Hanqaqa/Easyduino/Atmega328p Arduino Nano/ProductionFiles/PDFs/Schematic_Page_2.png

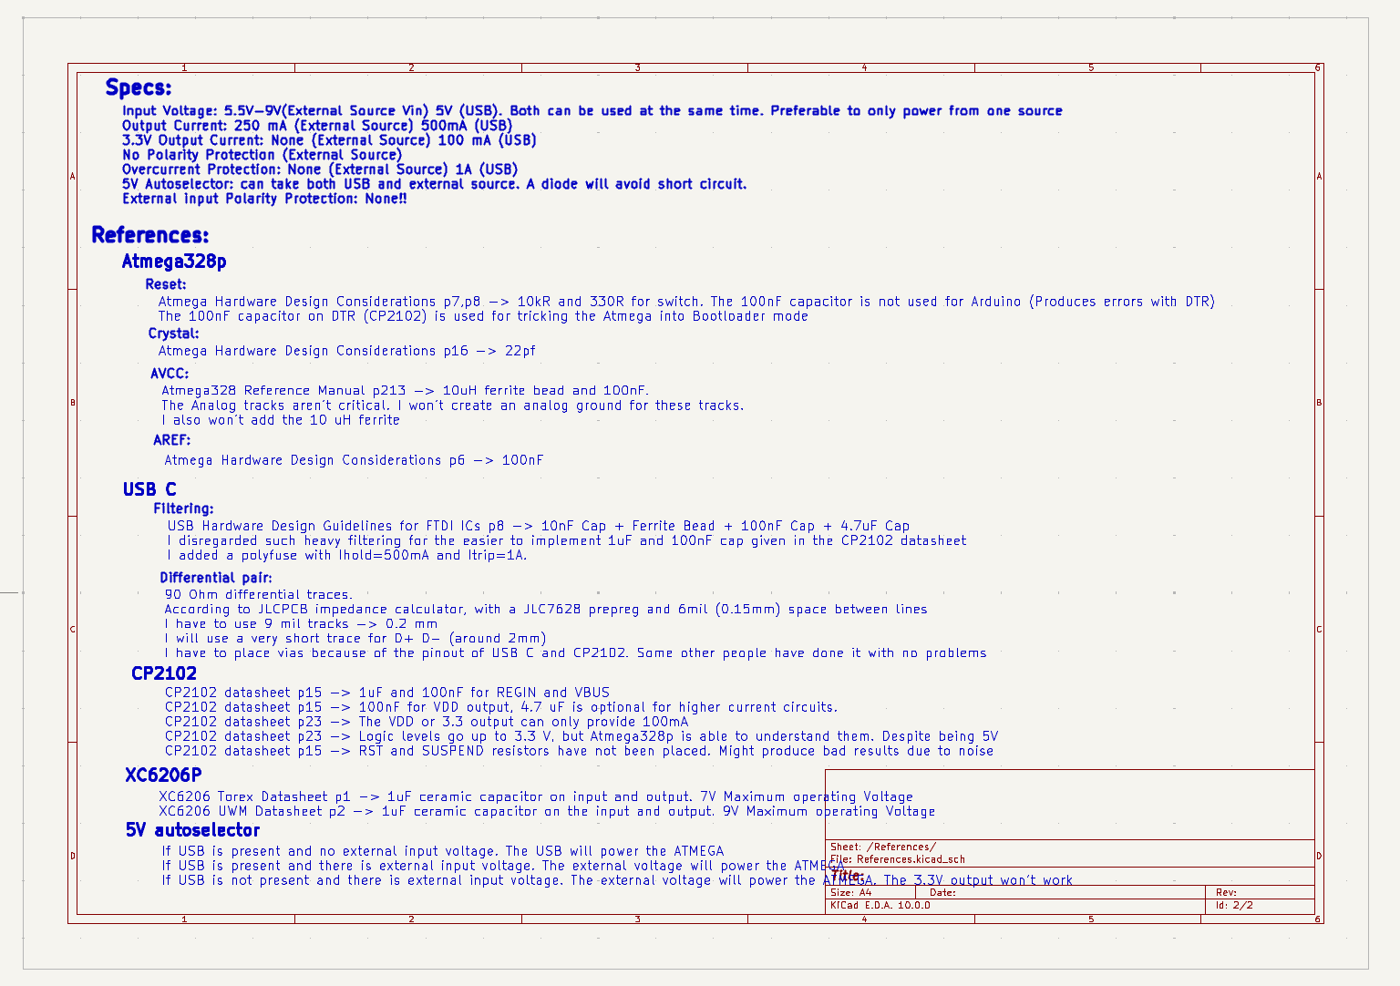
Atmega328p Arduino Nano/ProductionFiles/PDFs/Schematic_Page_2.png
