Hanqaqa/Easyduino/Atmega328p Arduino Nano/ProductionFiles/Photos/Easyduino Nano Bottom.jpg

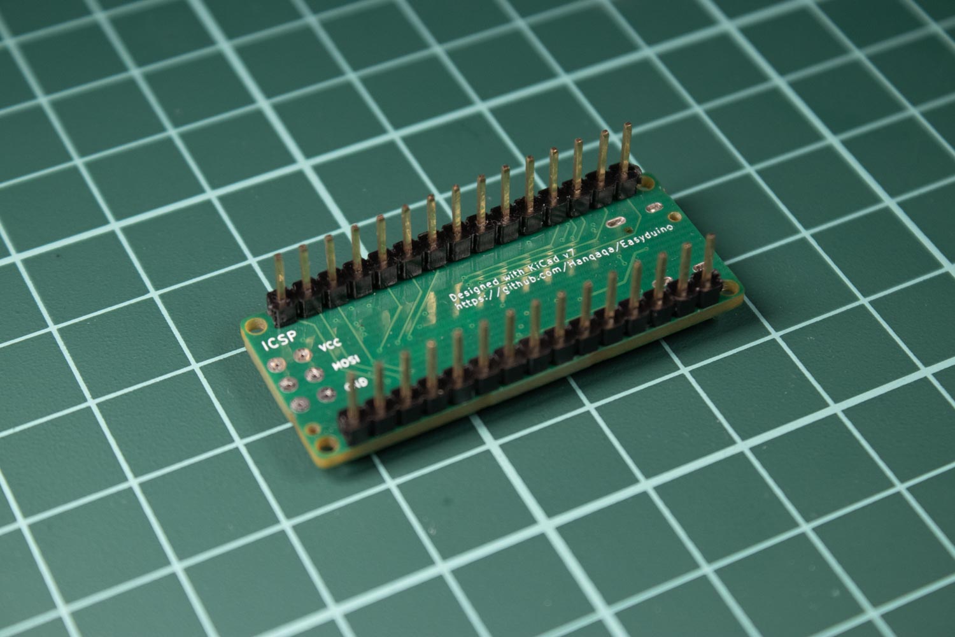
Atmega328p Arduino Nano/ProductionFiles/Photos/Easyduino Nano Bottom.jpg
