Hanqaqa/Easyduino/Atmega328p Arduino Nano/ProductionFiles/Photos/Easyduino Nano Detail 1.jpg

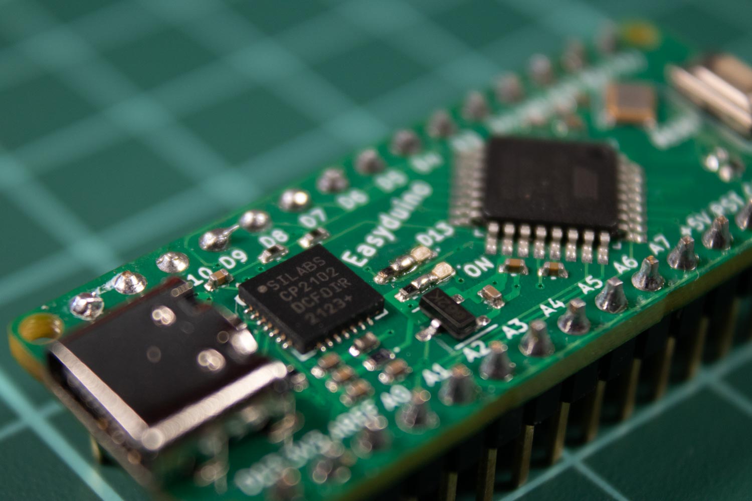
Atmega328p Arduino Nano/ProductionFiles/Photos/Easyduino Nano Detail 1.jpg
