Hanqaqa/Easyduino/Atmega328p Arduino Nano/ProductionFiles/Photos/Easyduino Nano Detail 2.jpg

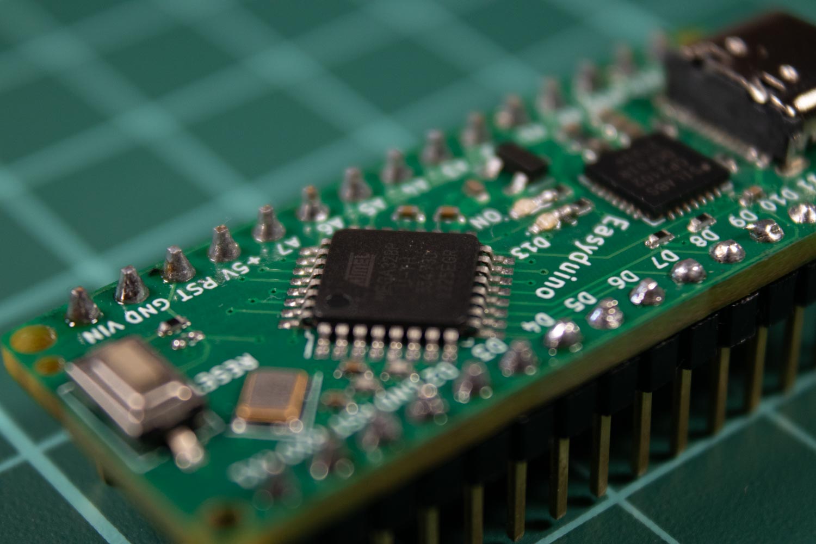
Atmega328p Arduino Nano/ProductionFiles/Photos/Easyduino Nano Detail 2.jpg
