Hanqaqa/Easyduino/Atmega328p Arduino Nano/ProductionFiles/Photos/Easyduino Nano Render Top.jpg

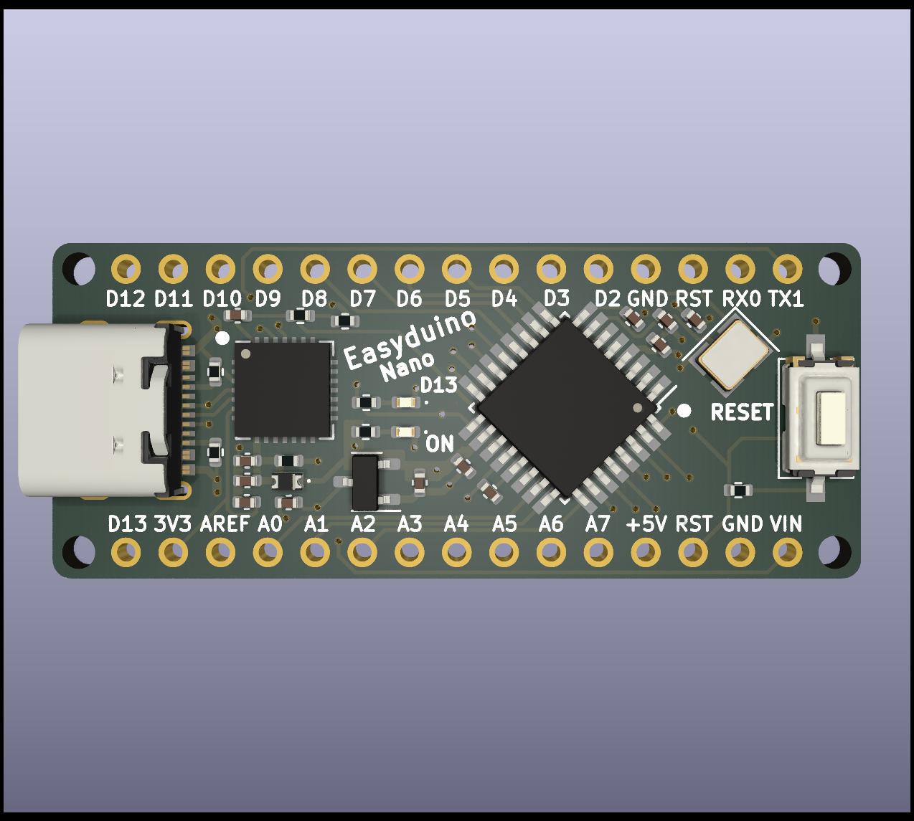
Atmega328p Arduino Nano/ProductionFiles/Photos/Easyduino Nano Render Top.jpg
