Hanqaqa/Easyduino/Atmega328p Arduino Nano/ProductionFiles/Photos/Easyduino Nano Top.jpg

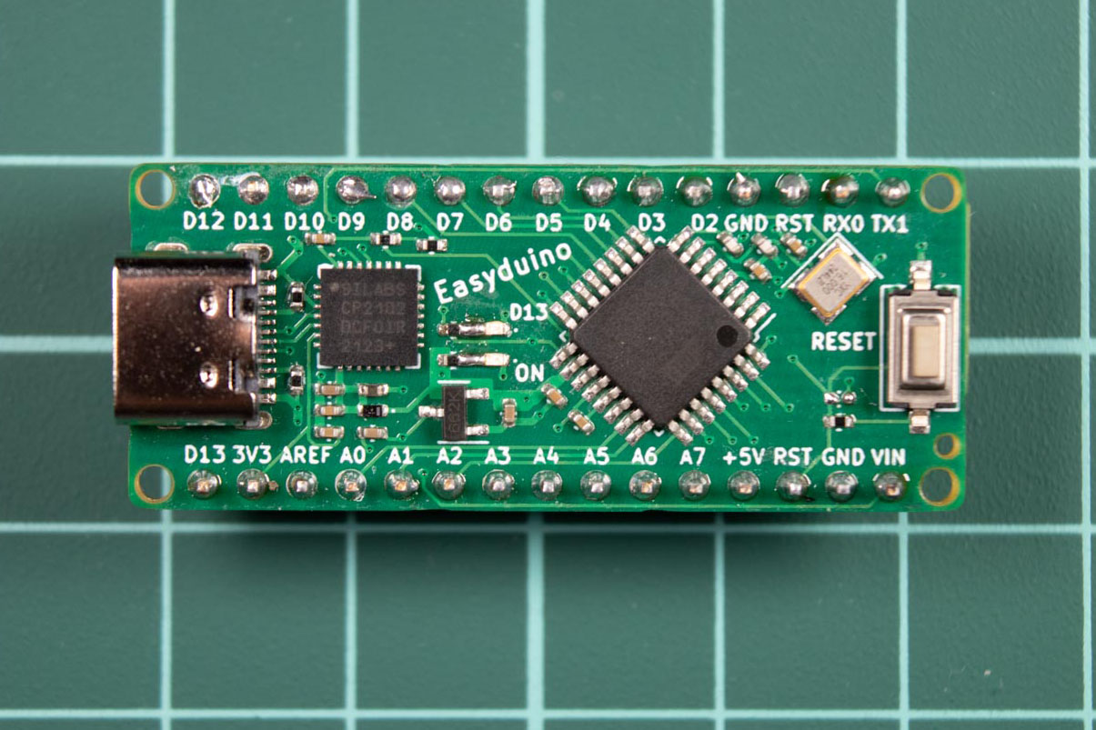
Atmega328p Arduino Nano/ProductionFiles/Photos/Easyduino Nano Top.jpg
