Hanqaqa/Easyduino/Atmega328p Arduino Uno/ProductionFiles/Photos/Easyduino Atmega Render Top.jpg

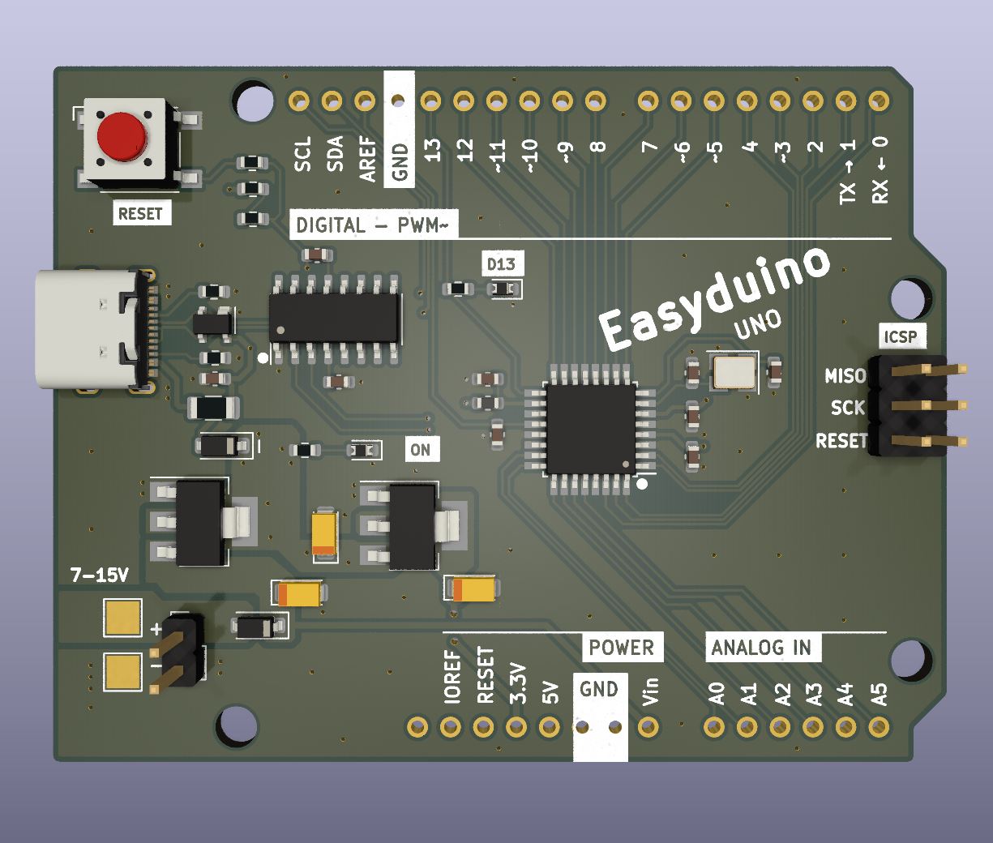
Atmega328p Arduino Uno/ProductionFiles/Photos/Easyduino Atmega Render Top.jpg
