Hanqaqa/Easyduino/Atmega328p Arduino Uno/ProductionFiles/Photos/Easyduino UNO Bottom.jpg

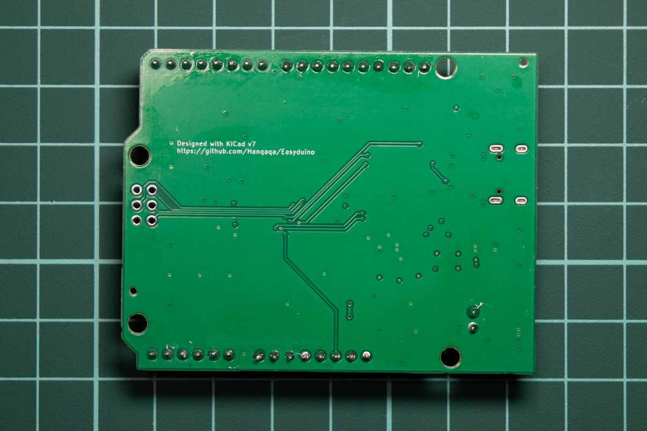
Atmega328p Arduino Uno/ProductionFiles/Photos/Easyduino UNO Bottom.jpg
