Hanqaqa/Easyduino/Atmega328p Arduino Uno/ProductionFiles/Photos/Easyduino UNO Detail 1.jpg

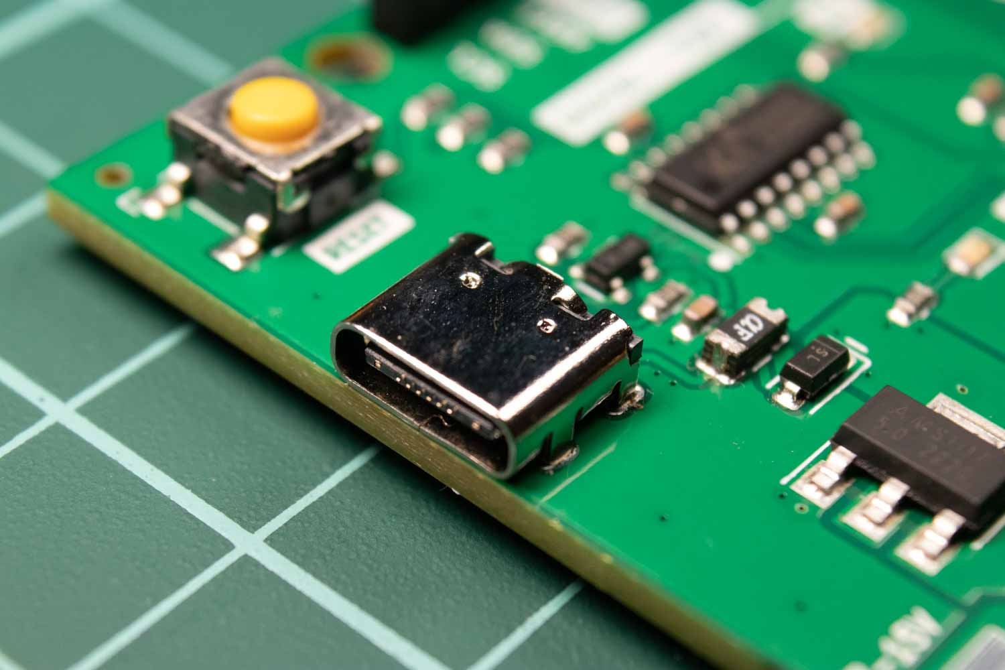
Atmega328p Arduino Uno/ProductionFiles/Photos/Easyduino UNO Detail 1.jpg
