Hanqaqa/Easyduino/Atmega328p Arduino Uno/ProductionFiles/Photos/Easyduino UNO Detail 4.jpg

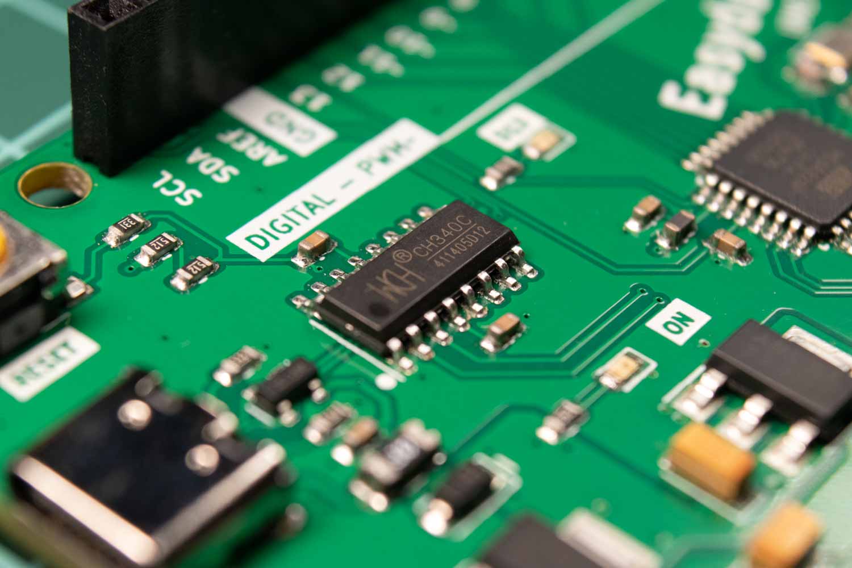
Atmega328p Arduino Uno/ProductionFiles/Photos/Easyduino UNO Detail 4.jpg
