Hanqaqa/Easyduino/Atmega328p Arduino Uno/ProductionFiles/Photos/Easyduino UNO Detail 5.jpg

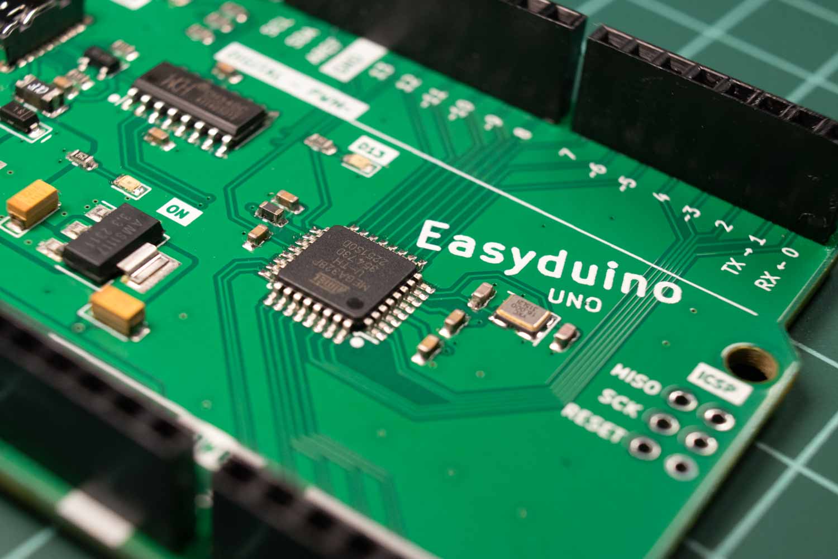
Atmega328p Arduino Uno/ProductionFiles/Photos/Easyduino UNO Detail 5.jpg
