Hanqaqa/Easyduino/Atmega328p Arduino Uno/ProductionFiles/Photos/Easyduino UNO Top.jpg

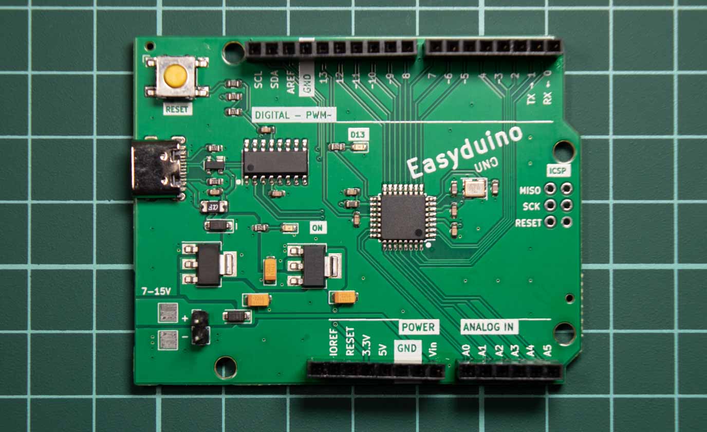
Atmega328p Arduino Uno/ProductionFiles/Photos/Easyduino UNO Top.jpg
