Hanqaqa/Easyduino/ESP32/ProductionFiles/PDFs/Schematic_Page_2.png

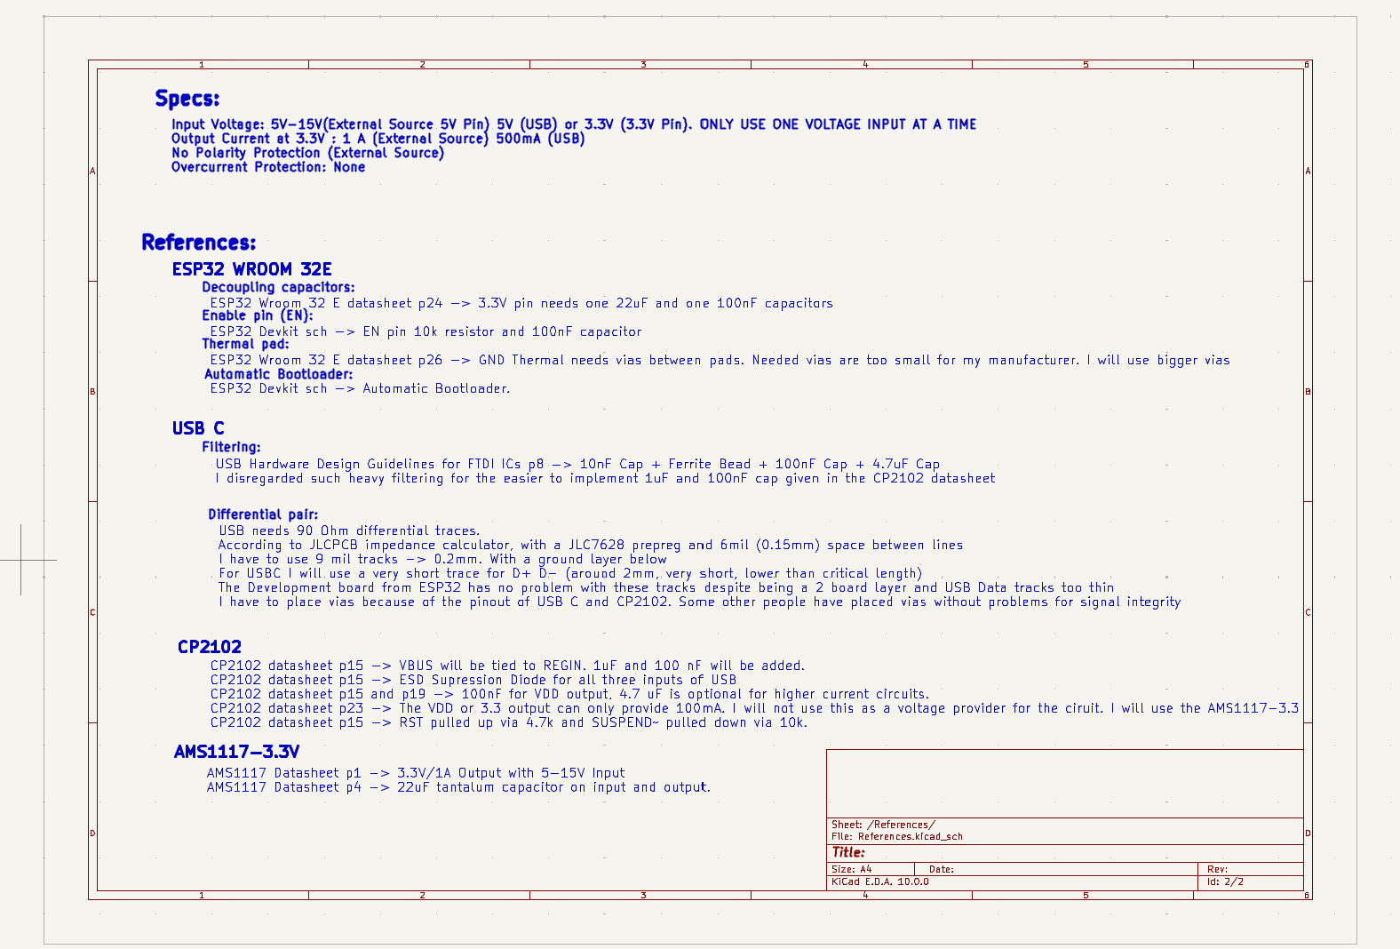
ESP32/ProductionFiles/PDFs/Schematic_Page_2.png
