Hanqaqa/Easyduino/ESP32/ProductionFiles/Photos/Easyduino ESP32 Bottom.jpg

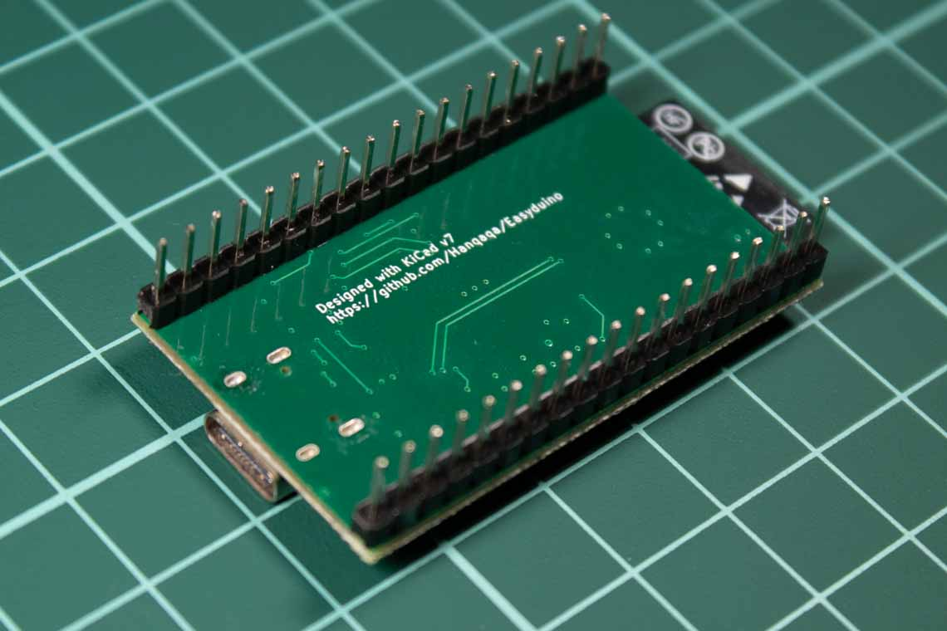
ESP32/ProductionFiles/Photos/Easyduino ESP32 Bottom.jpg
