Hanqaqa/Easyduino/ESP32/ProductionFiles/Photos/Easyduino ESP32 Detail 1.jpg

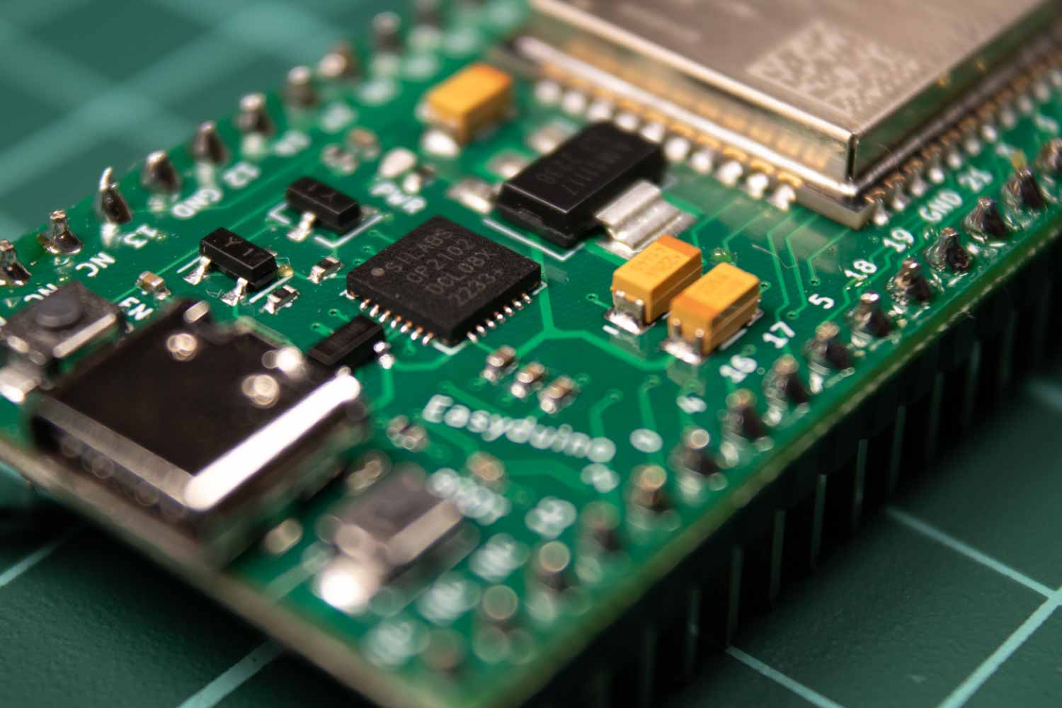
ESP32/ProductionFiles/Photos/Easyduino ESP32 Detail 1.jpg
