Hanqaqa/Easyduino/ESP32/ProductionFiles/Photos/Easyduino ESP32 Render Top.jpg

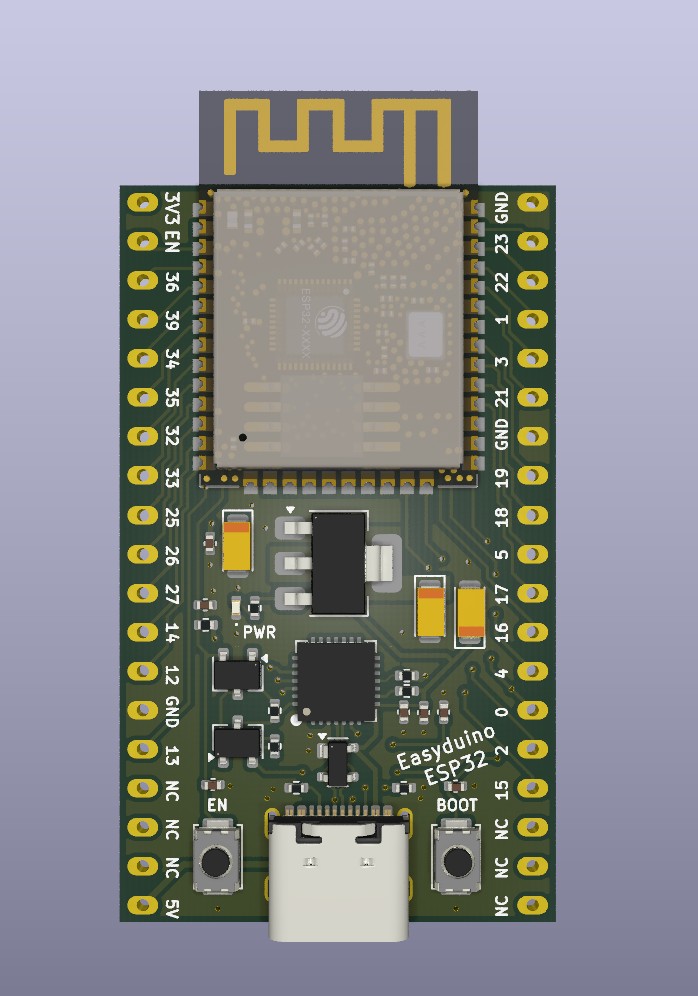
ESP32/ProductionFiles/Photos/Easyduino ESP32 Render Top.jpg
