Hanqaqa/Easyduino/ESP32/ProductionFiles/Photos/Easyduino ESP32 Top.jpg

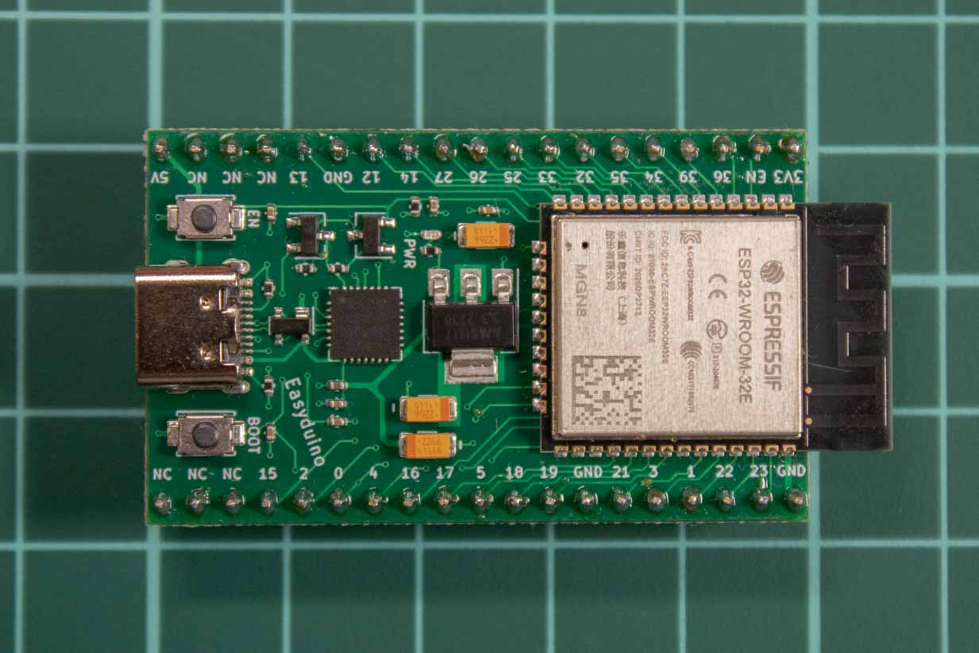
ESP32/ProductionFiles/Photos/Easyduino ESP32 Top.jpg
