Hanqaqa/Easyduino/ESP32/ProductionFiles/Photos/Easyduino ESP32 VScoring.jpg

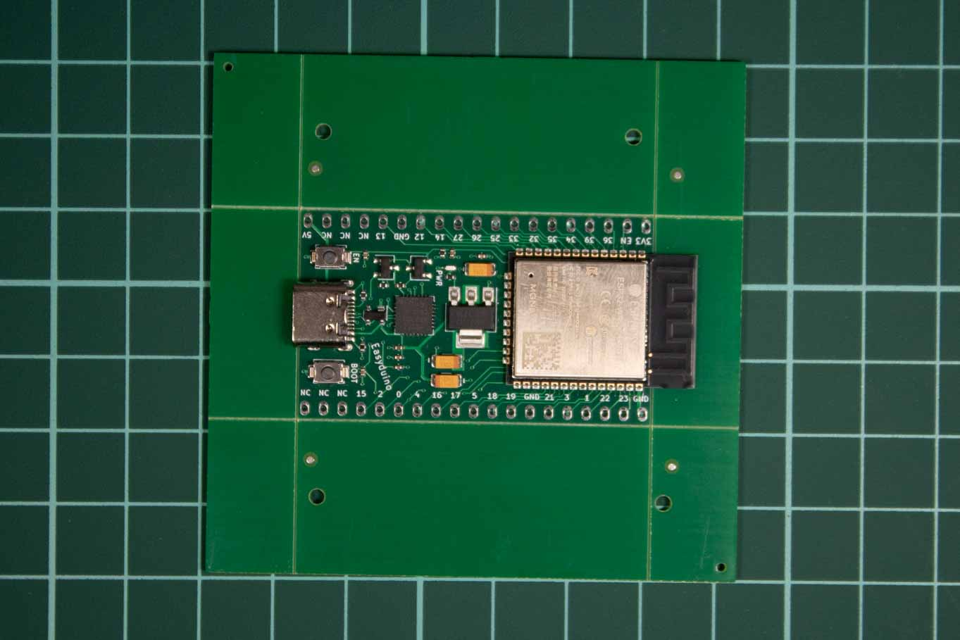
ESP32/ProductionFiles/Photos/Easyduino ESP32 VScoring.jpg
