Hanqaqa/Easyduino/ESP32S3/ProductionFiles/Photos/Easyduino ESP32S3 Bottom.jpg

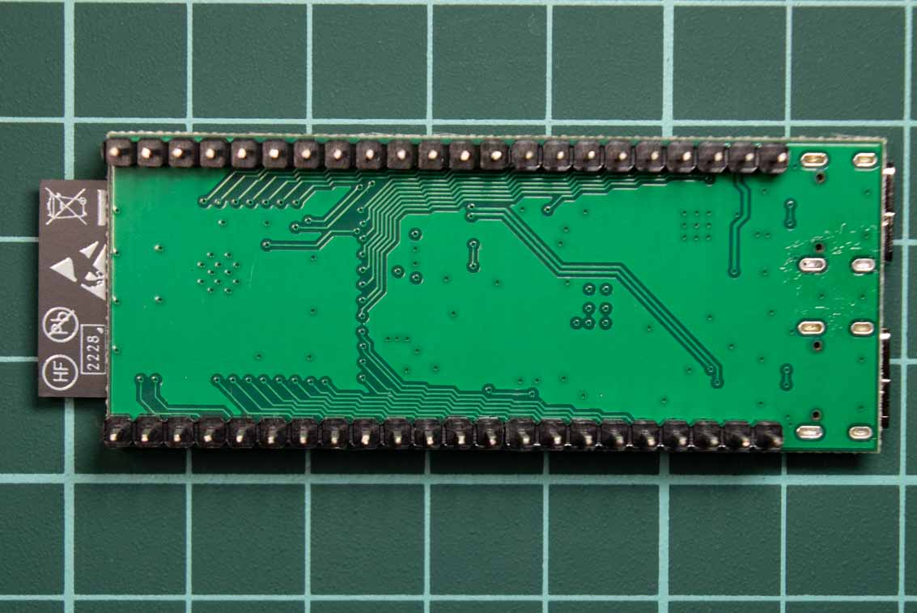
ESP32S3/ProductionFiles/Photos/Easyduino ESP32S3 Bottom.jpg
