Hanqaqa/Easyduino/ESP32S3/ProductionFiles/Photos/Easyduino ESP32S3 Detail 1.jpg

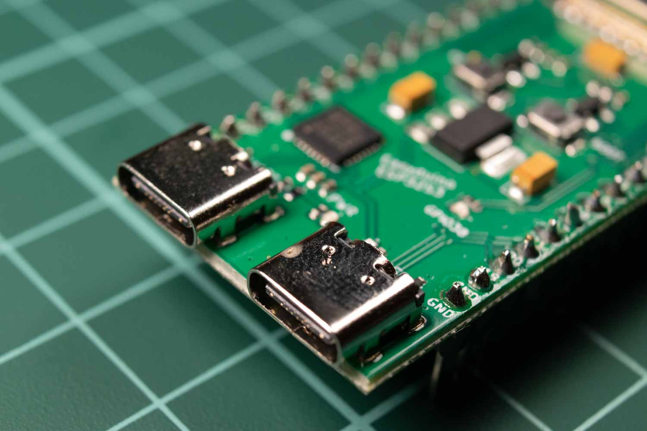
ESP32S3/ProductionFiles/Photos/Easyduino ESP32S3 Detail 1.jpg
