Hanqaqa/Easyduino/ESP32S3/ProductionFiles/Photos/Easyduino ESP32S3 Detail 2.jpg

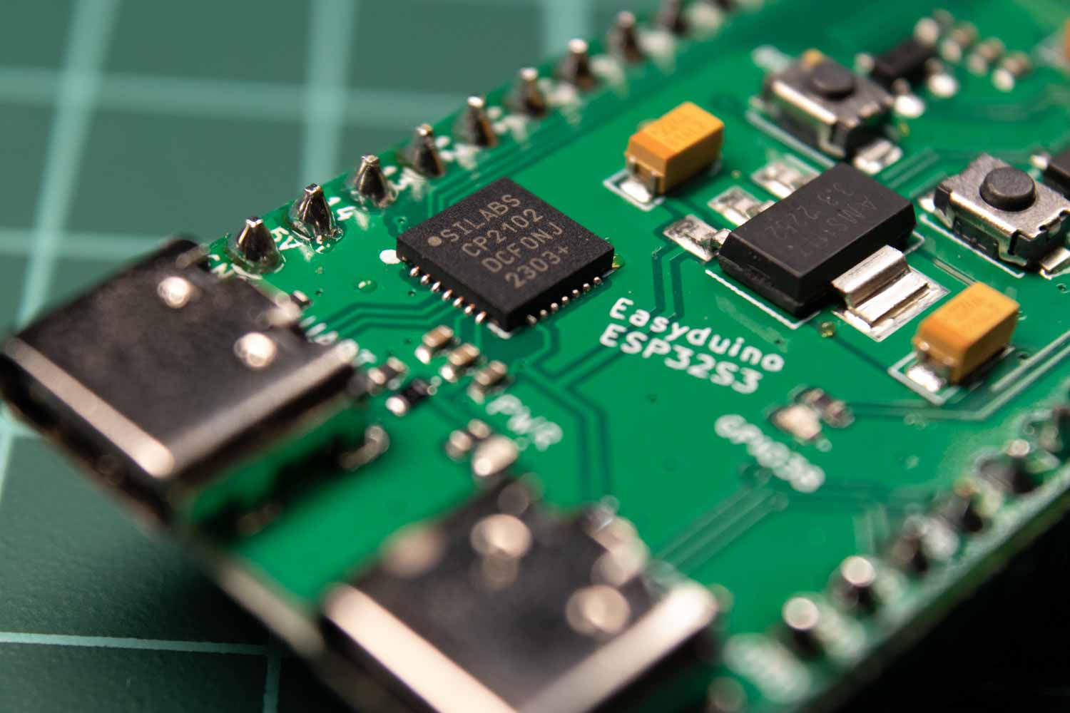
ESP32S3/ProductionFiles/Photos/Easyduino ESP32S3 Detail 2.jpg
