Hanqaqa/Easyduino/ESP32S3/ProductionFiles/Photos/Easyduino ESP32S3 Detail 3.jpg

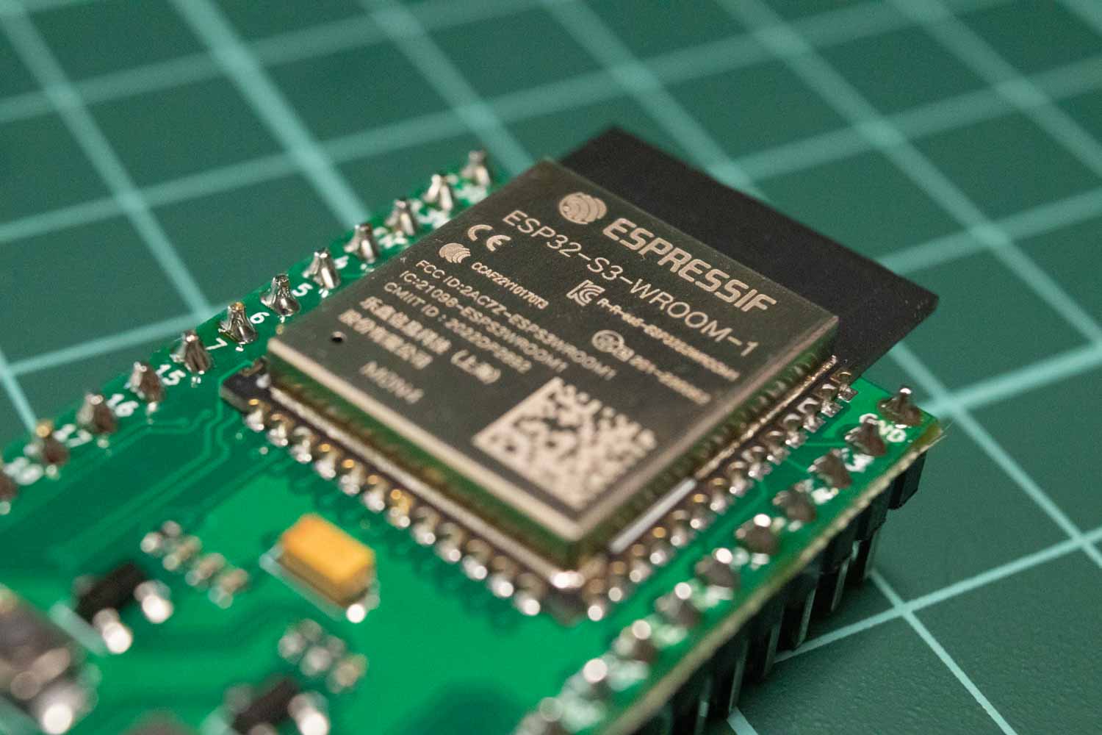
ESP32S3/ProductionFiles/Photos/Easyduino ESP32S3 Detail 3.jpg
