Hanqaqa/Easyduino/ESP32S3/ProductionFiles/Photos/Easyduino ESP32S3 Render Top.JPG

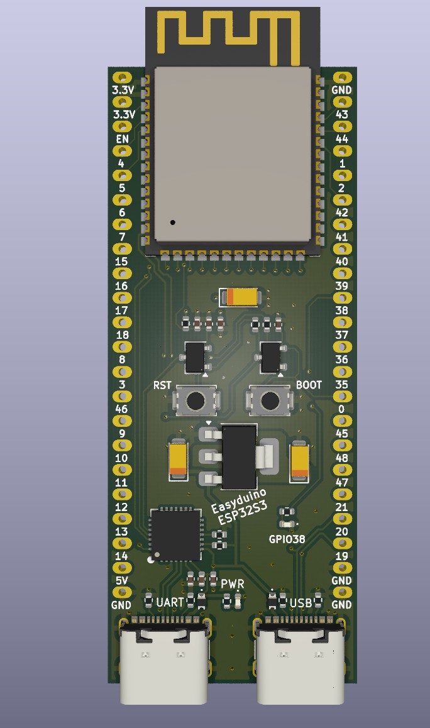
ESP32S3/ProductionFiles/Photos/Easyduino ESP32S3 Render Top.JPG
