Hanqaqa/Easyduino/ESP32S3/ProductionFiles/Photos/Easyduino ESP32S3 Top.jpg

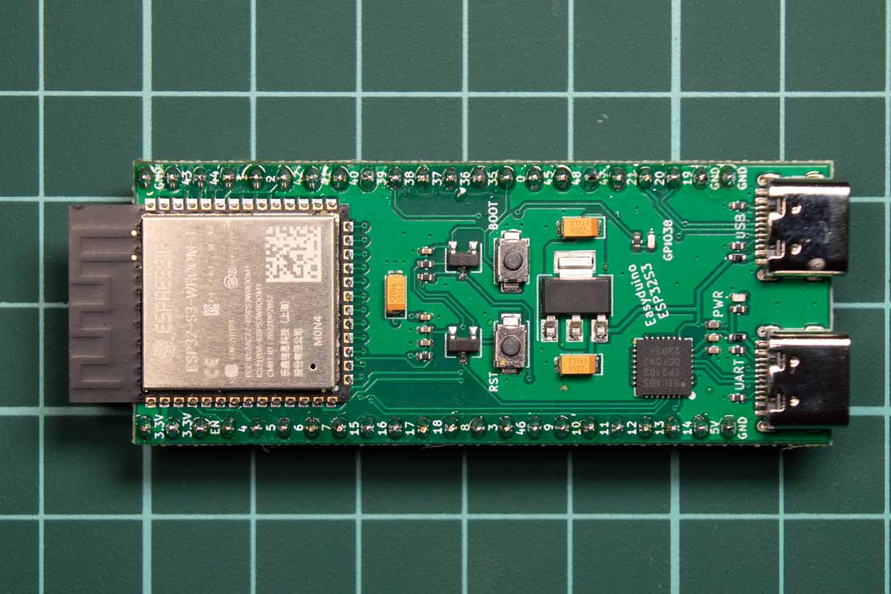
ESP32S3/ProductionFiles/Photos/Easyduino ESP32S3 Top.jpg
