Hanqaqa/Easyduino/ESP32S3/ProductionFiles/Photos/Screenshot 2026-04-21 203034.jpg

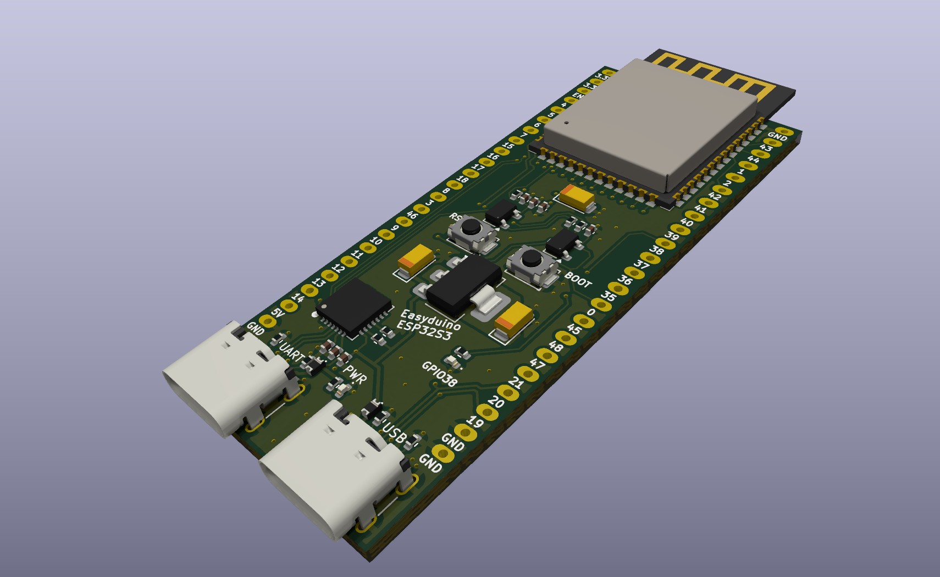
ESP32S3/ProductionFiles/Photos/Screenshot 2026-04-21 203034.jpg
