Hanqaqa/Easyduino/Raspberry Pi Pico 2040/ProductionFiles/PDFs/Schematic_Page_2.png

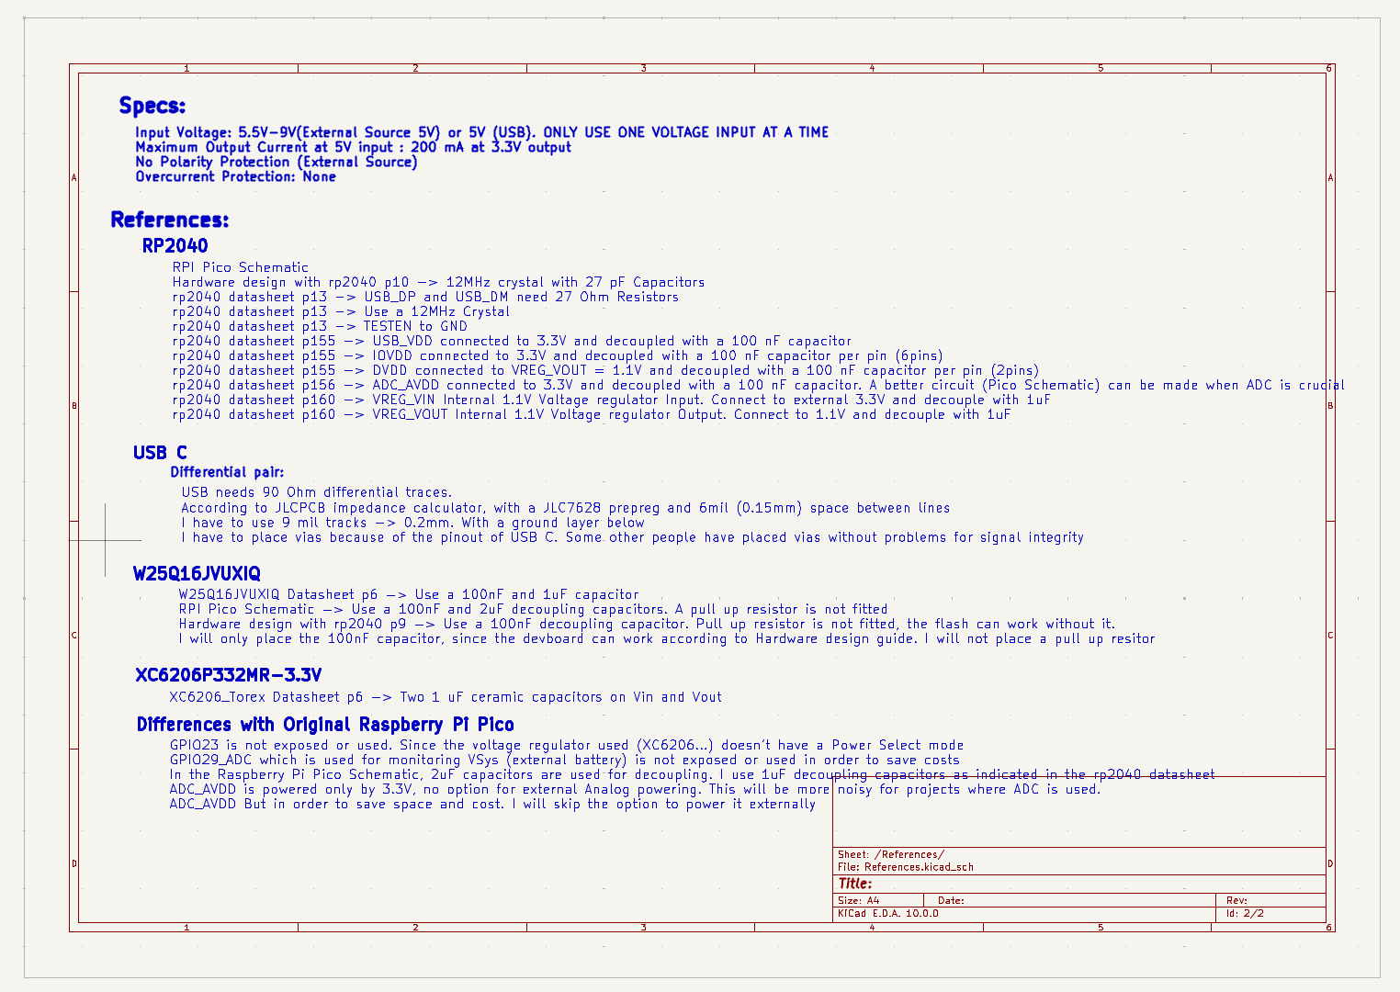
Raspberry Pi Pico 2040/ProductionFiles/PDFs/Schematic_Page_2.png
