Hanqaqa/Easyduino/Raspberry Pi Pico 2040/ProductionFiles/Photos/Easyduino RP2040 Bottom.jpg

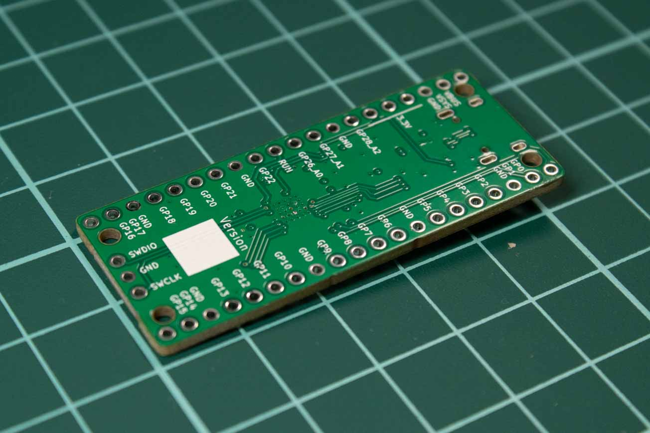
Raspberry Pi Pico 2040/ProductionFiles/Photos/Easyduino RP2040 Bottom.jpg
