Hanqaqa/Easyduino/Raspberry Pi Pico 2040/ProductionFiles/Photos/Easyduino RP2040 Detail 1.jpg

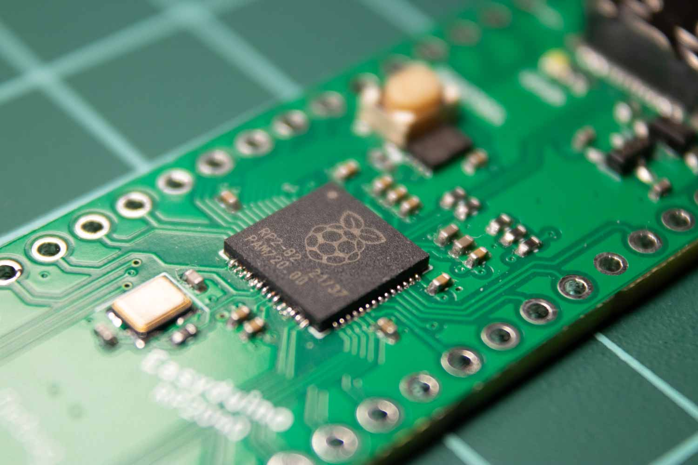
Raspberry Pi Pico 2040/ProductionFiles/Photos/Easyduino RP2040 Detail 1.jpg
