Hanqaqa/Easyduino/Raspberry Pi Pico 2040/ProductionFiles/Photos/Easyduino RP2040 Detail 2.jpg

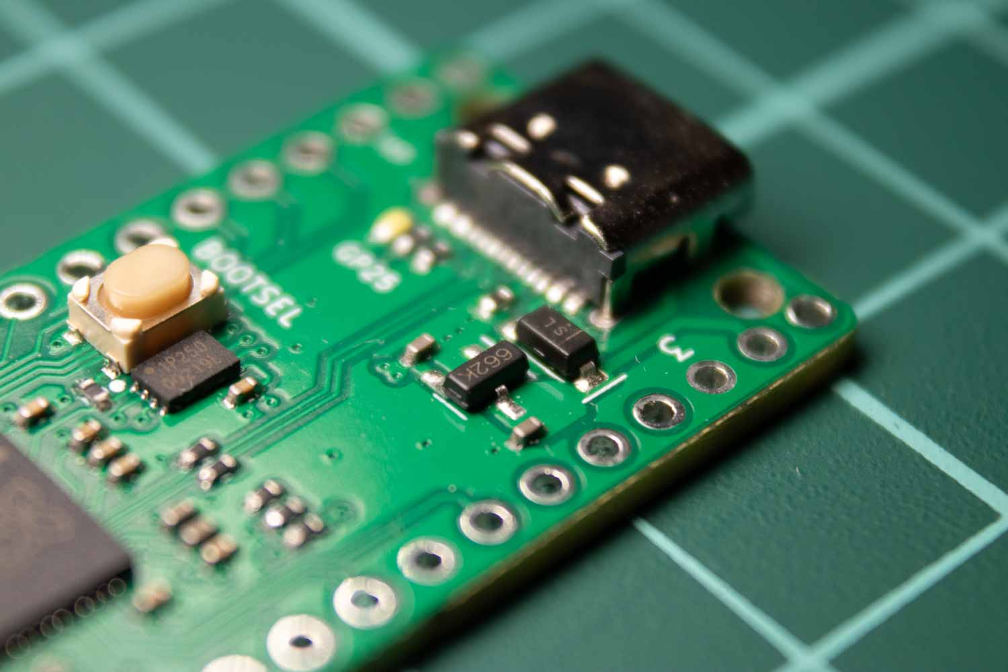
Raspberry Pi Pico 2040/ProductionFiles/Photos/Easyduino RP2040 Detail 2.jpg
