Hanqaqa/Easyduino/Raspberry Pi Pico 2040/ProductionFiles/Photos/Easyduino RP2040 Detail 3.jpg

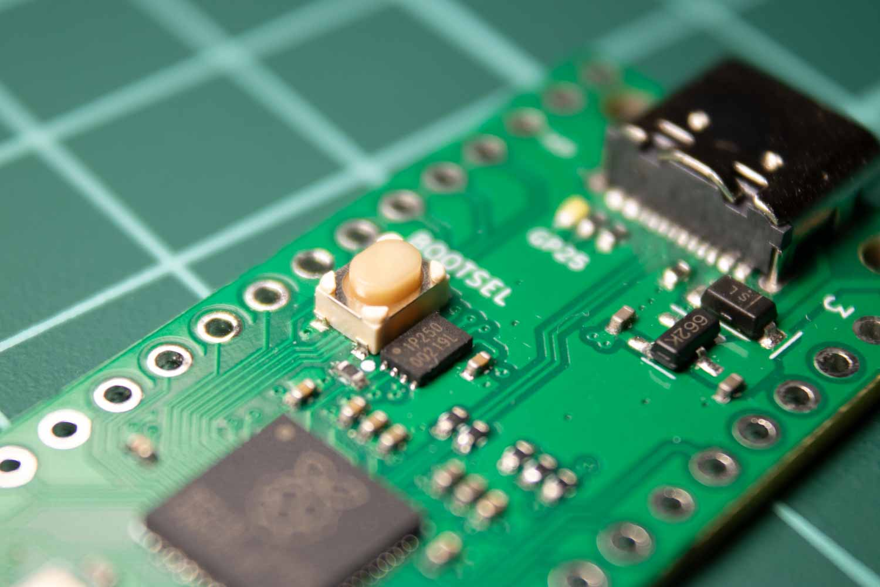
Raspberry Pi Pico 2040/ProductionFiles/Photos/Easyduino RP2040 Detail 3.jpg
