Hanqaqa/Easyduino/Raspberry Pi Pico 2040/ProductionFiles/Photos/Easyduino RP2040 Render Top.jpg

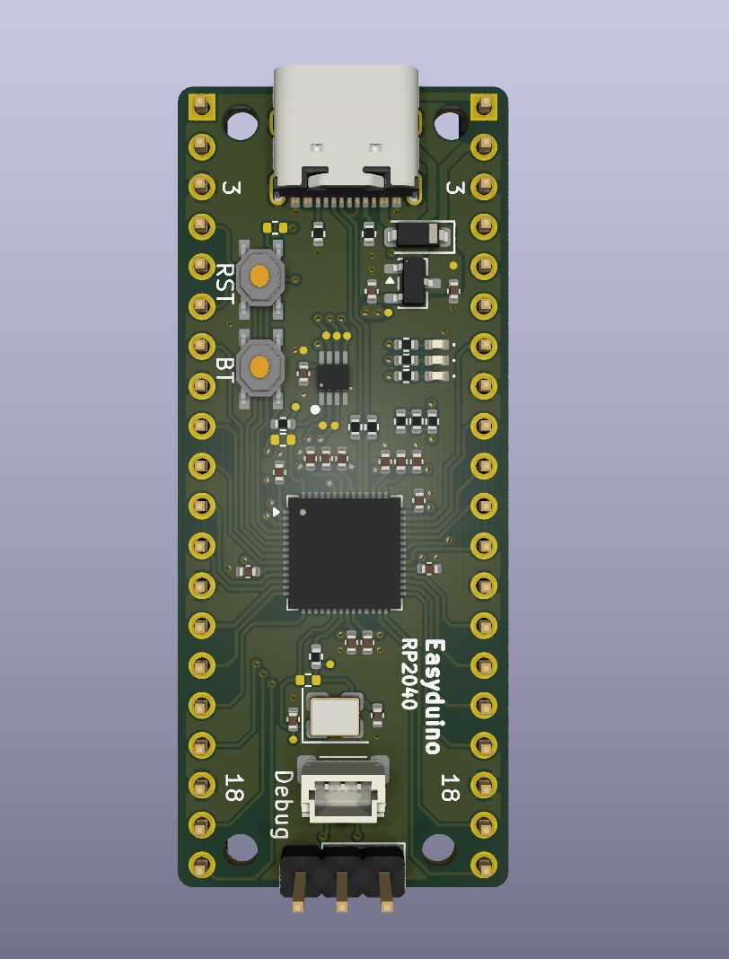
Raspberry Pi Pico 2040/ProductionFiles/Photos/Easyduino RP2040 Render Top.jpg
