Hanqaqa/Easyduino/STM32F103 Bluepill/ProductionFiles/Photos/Easyduino STM32F1 Detail3.jpg

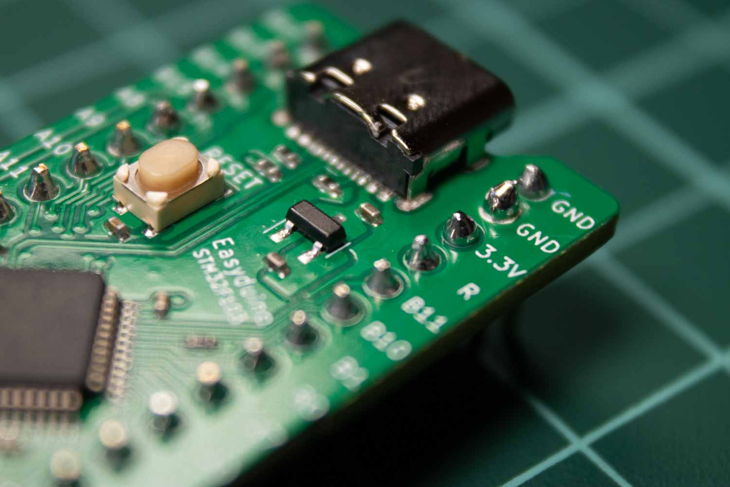
STM32F103 Bluepill/ProductionFiles/Photos/Easyduino STM32F1 Detail3.jpg
