Hanqaqa/Easyduino/STM32F103 Bluepill/ProductionFiles/Photos/Easyduino STM32F103 Render Top.jpg

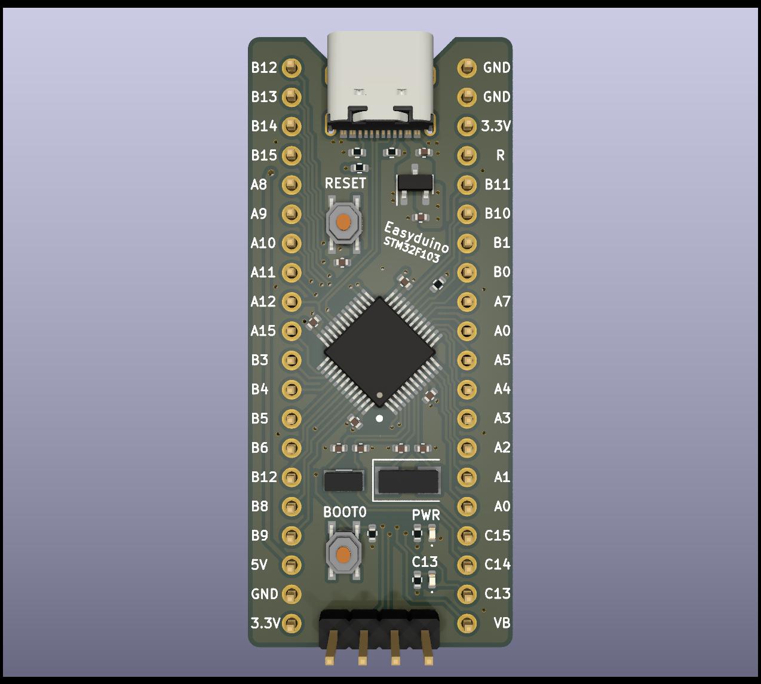
STM32F103 Bluepill/ProductionFiles/Photos/Easyduino STM32F103 Render Top.jpg
