Hanqaqa/Easyduino/ESP32/ProductionFiles/PDFs/Schematic.pdf

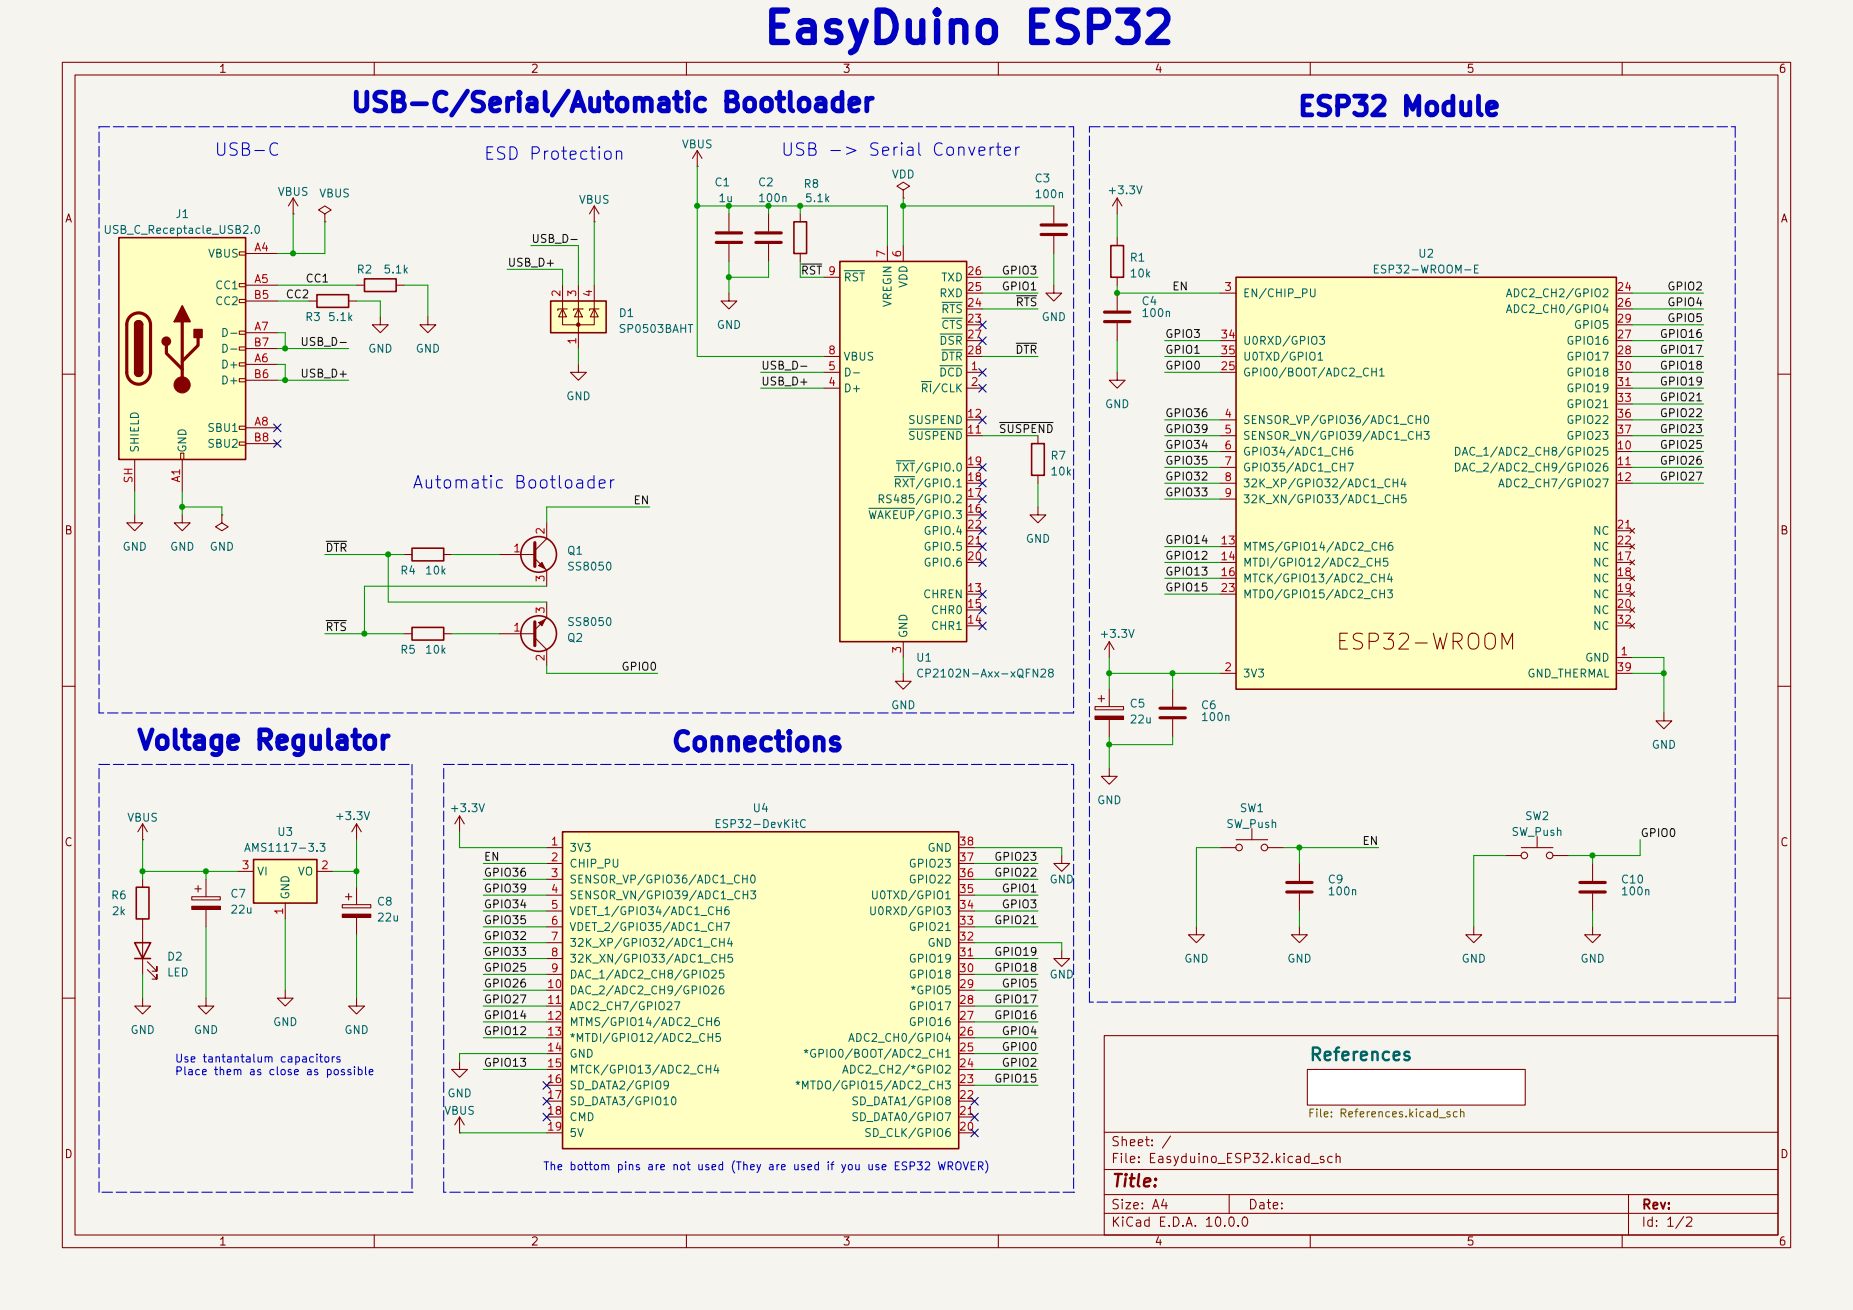
[picture p99: page 1]

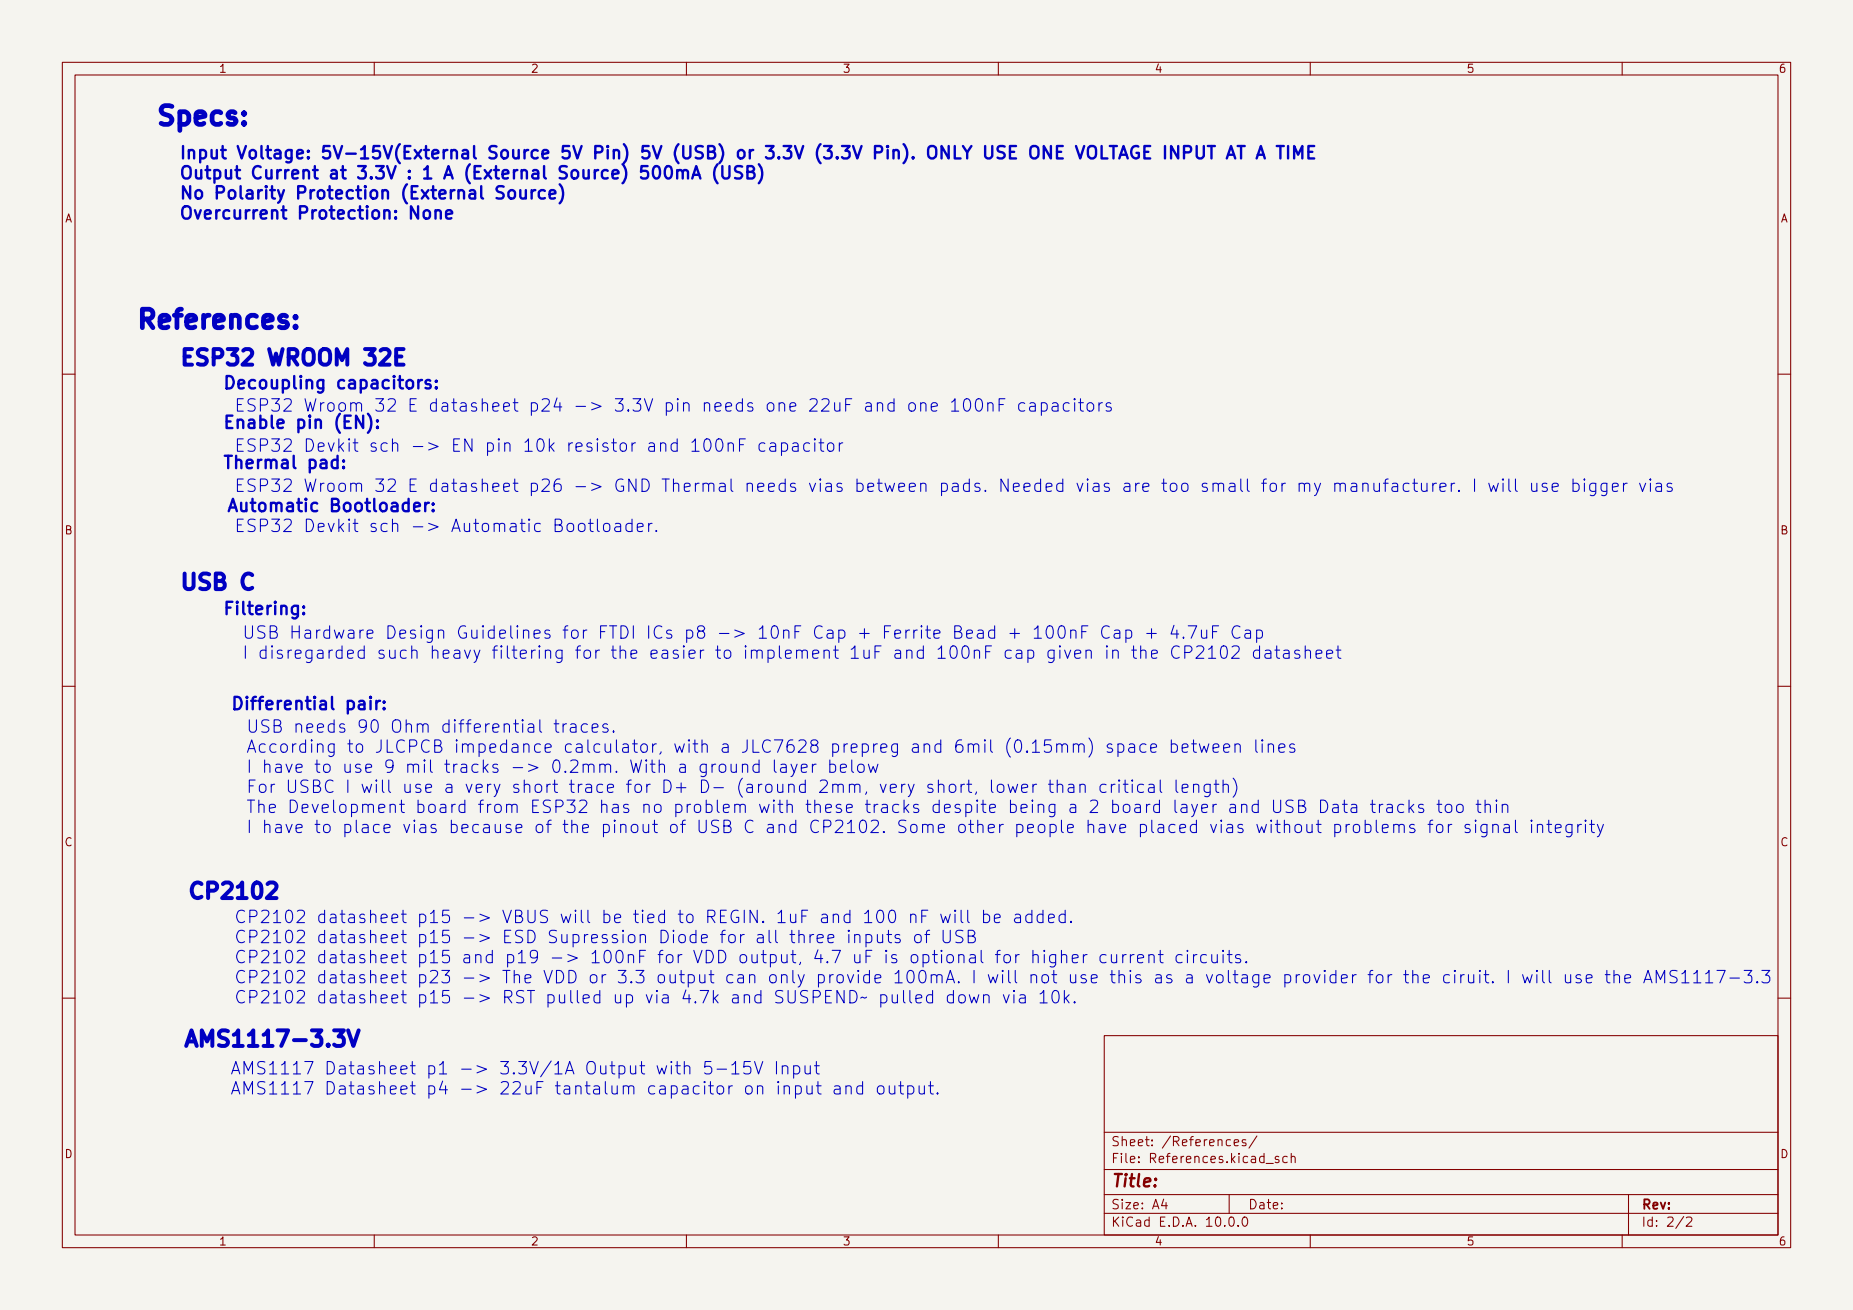
[picture p100: page 2]
